JustinYa/AquaticCatchPredictor/data/202 User Study.jpg

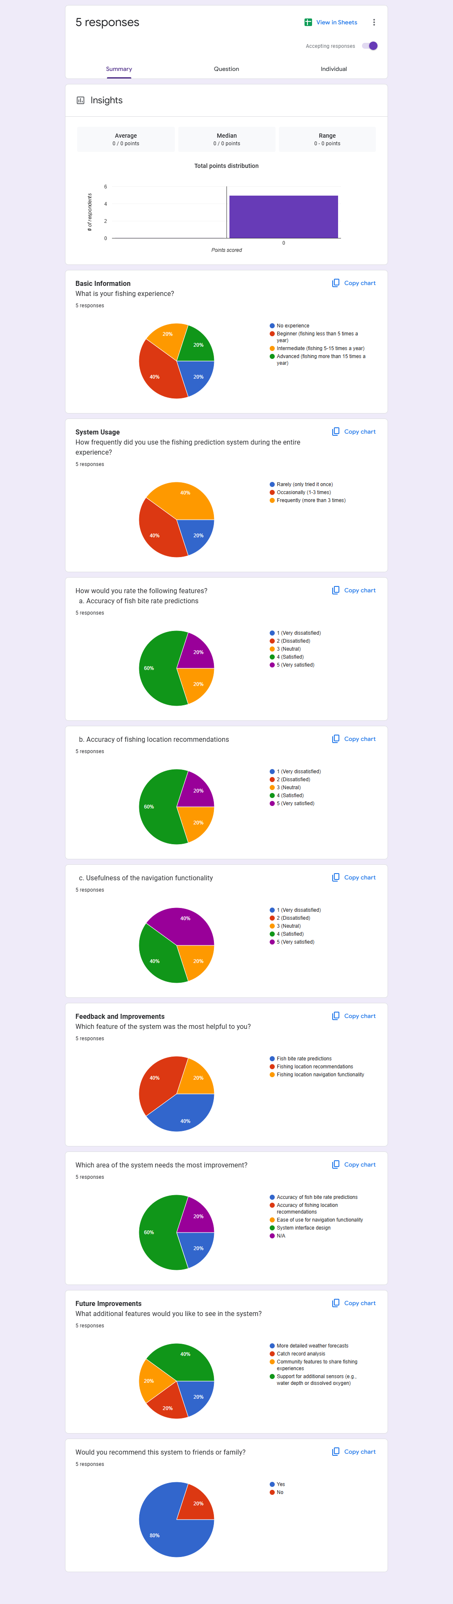
data/202 User Study.jpg
